Debanx3/Drishtikon/Elements/bix.png

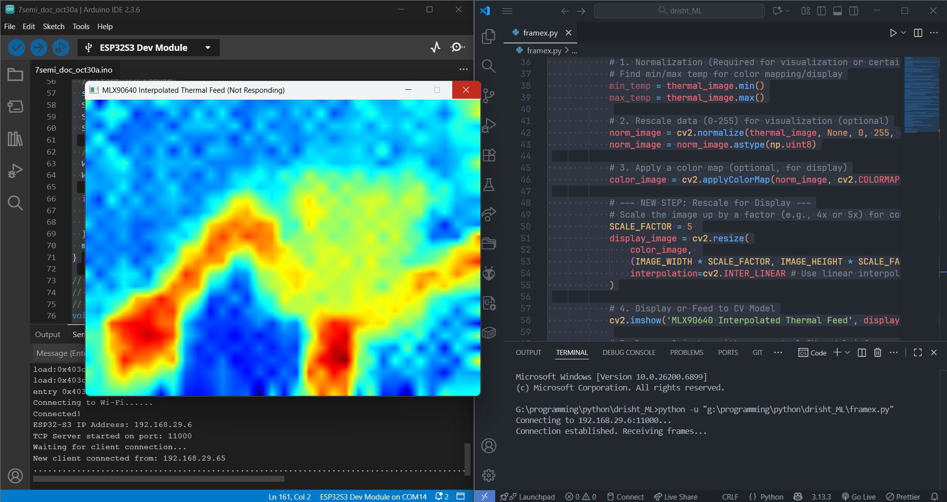
Elements/bix.png
