Debanx3/Drishtikon/Elements/boba.png

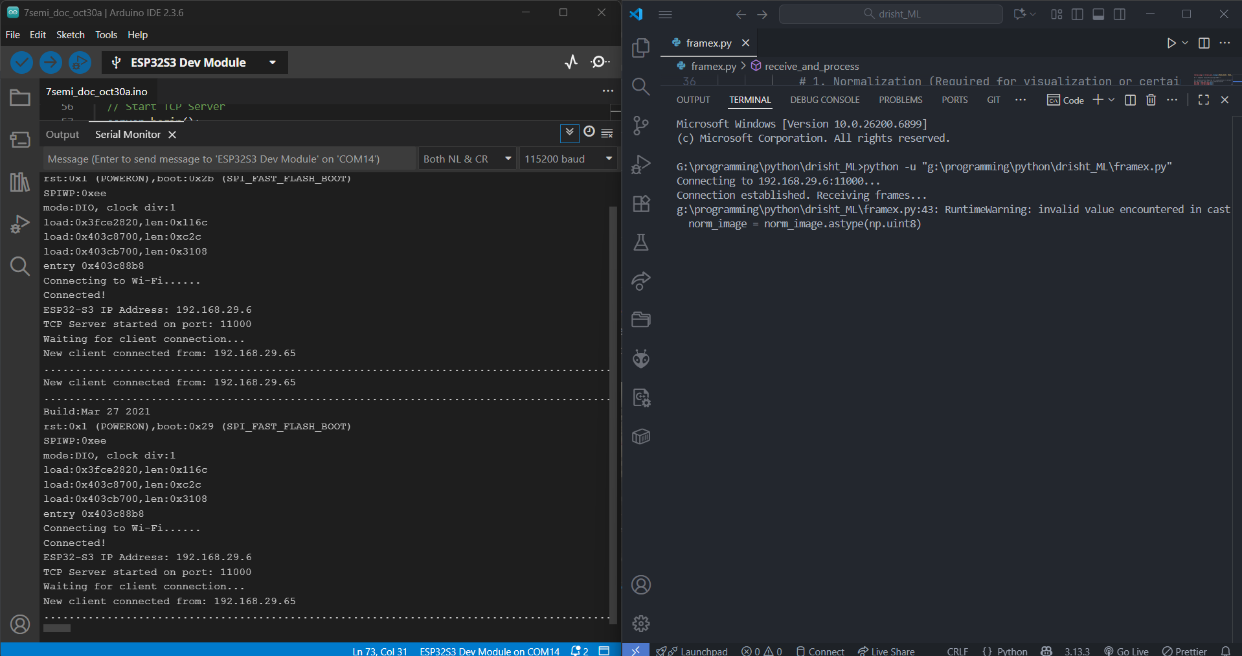
Elements/boba.png
