Debanx3/Drishtikon/Elements/feed_2.png

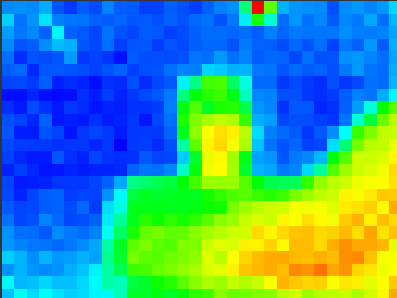
Elements/feed_2.png
