Debanx3/Drishtikon/Source_Code/Controller unit/Controller.jpg

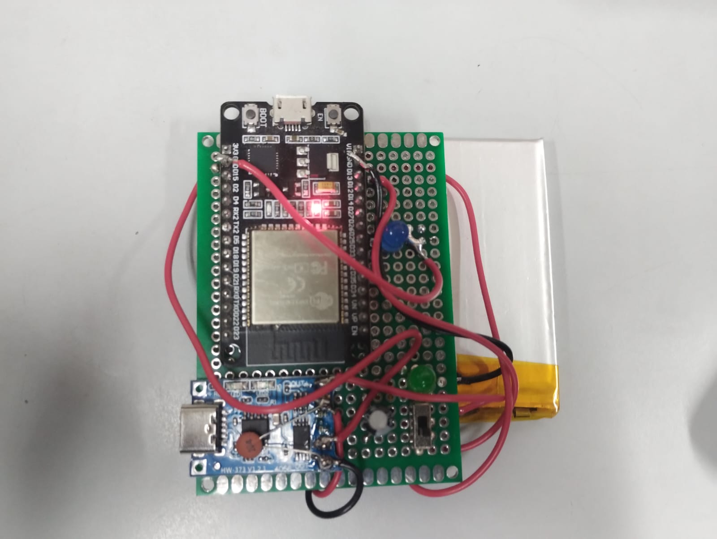
Source_Code/Controller unit/Controller.jpg
