Debanx3/Drishtikon/Source_Code/Controller unit/pros_c.png

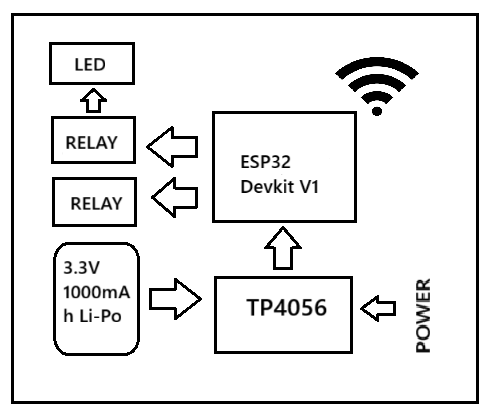
Source_Code/Controller unit/pros_c.png
