Debanx3/Drishtikon/Source_Code/Elements/A/controller.jpg

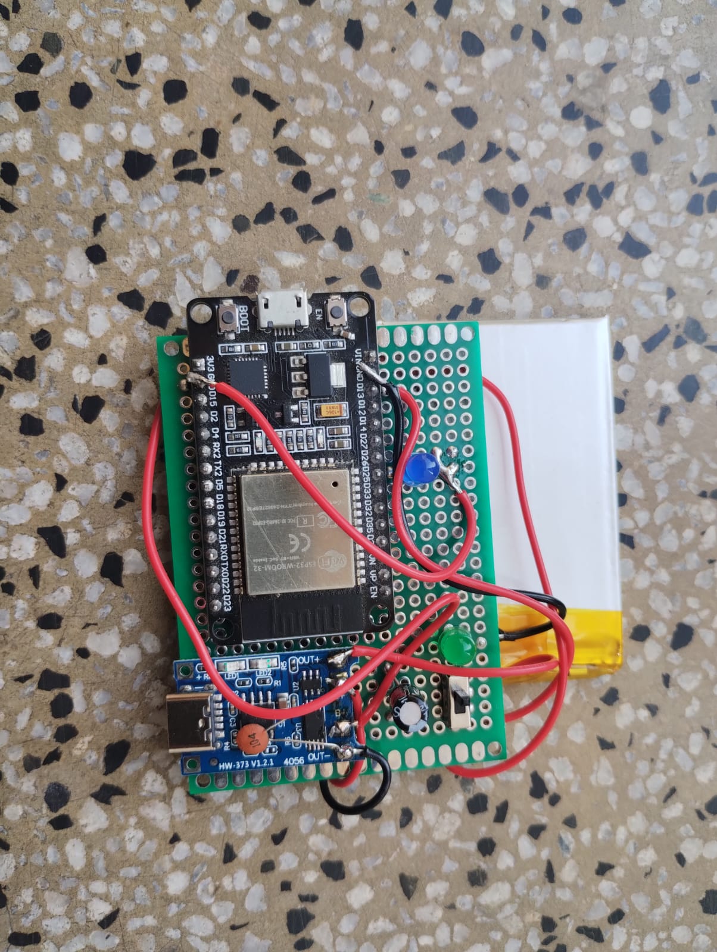
Source_Code/Elements/A/controller.jpg
