Debanx3/Drishtikon/Source_Code/Elements/A/full.jpg

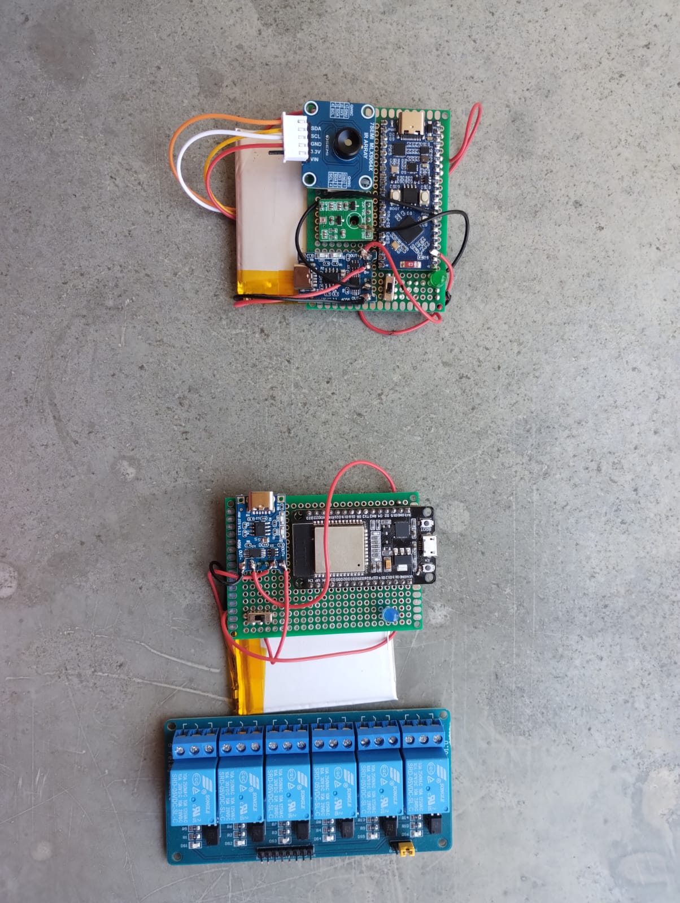
Source_Code/Elements/A/full.jpg
