Debanx3/Drishtikon/Source_Code/Elements/A/widget.jpg

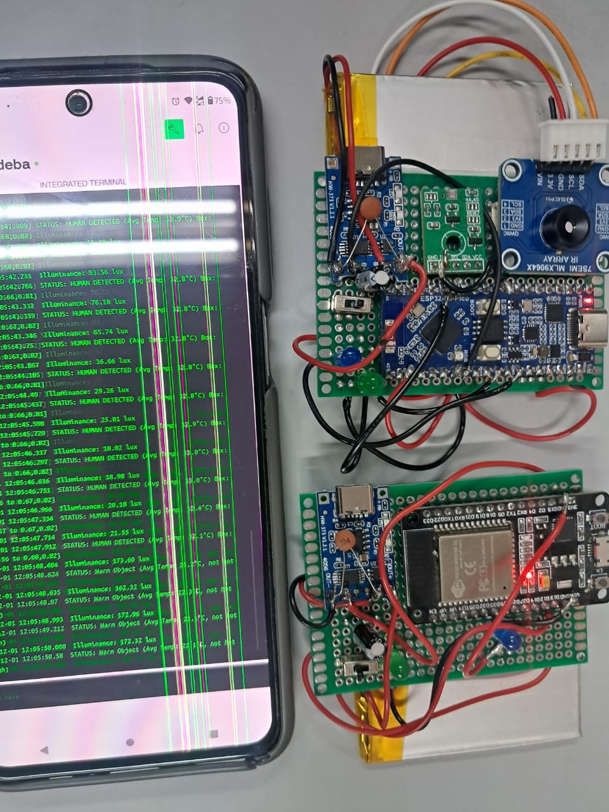
Source_Code/Elements/A/widget.jpg
