Debanx3/Drishtikon/Source_Code/Frontend/drishtikon/bixo1.png

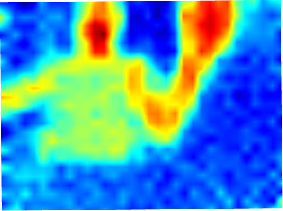
Source_Code/Frontend/drishtikon/bixo1.png
