Debanx3/Drishtikon/Source_Code/Frontend/drishtikon/greydata.png

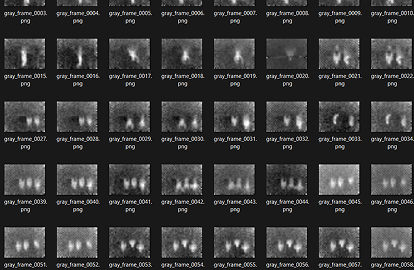
Source_Code/Frontend/drishtikon/greydata.png
