Debanx3/Drishtikon/Source_Code/Processing unit/Processing.jpg

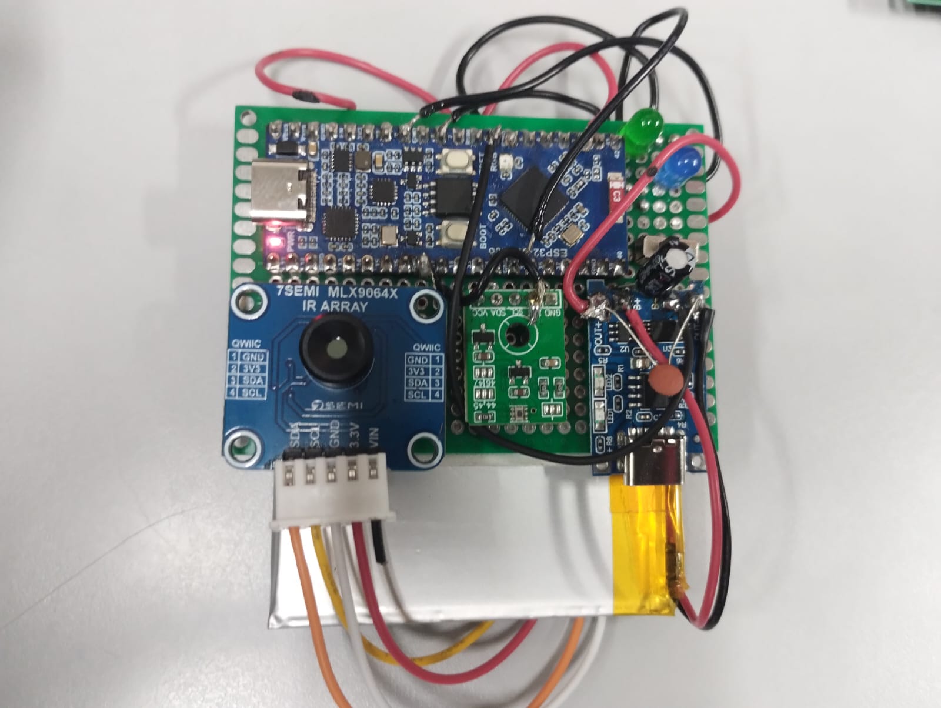
Source_Code/Processing unit/Processing.jpg
