Debanx3/Drishtikon/Source_Code/Elements/A/model_detected_results.jpg

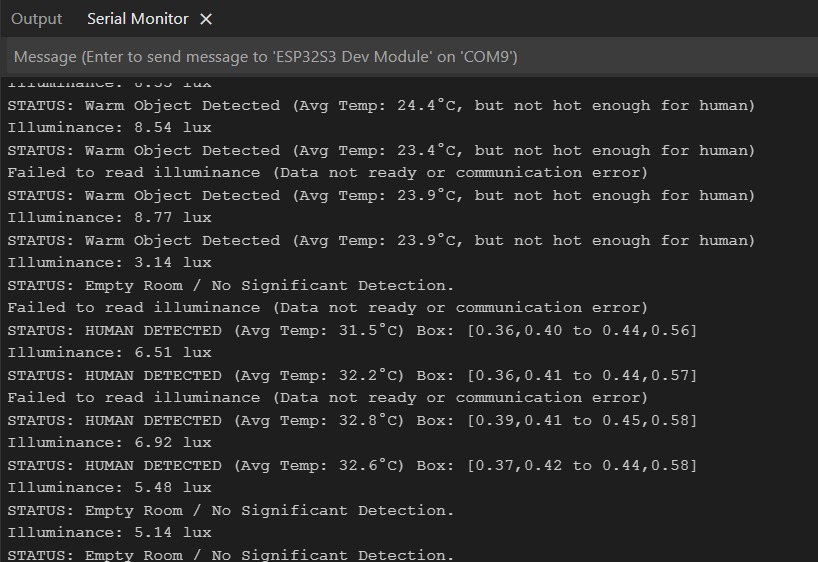
Source_Code/Elements/A/model_detected_results.jpg
