Debanx3/Drishtikon/Source_Code/Elements/A/model_detected_results_2.jpg

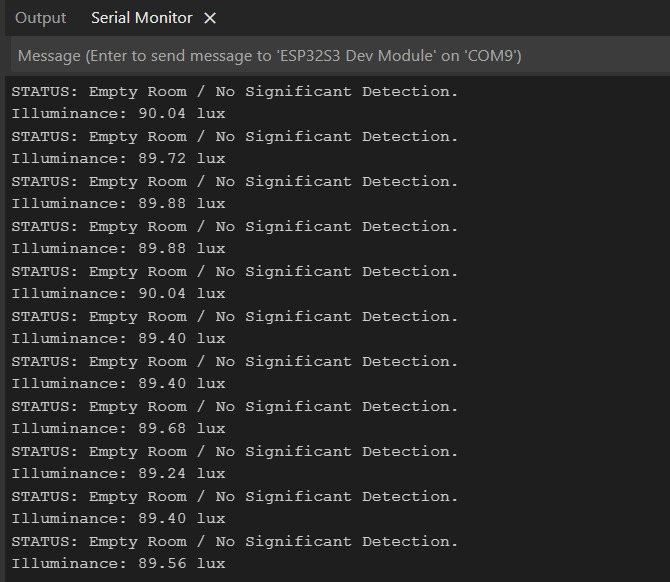
Source_Code/Elements/A/model_detected_results_2.jpg
